digitalinvitro/micro6502/pic/load_bin_menu.jpg

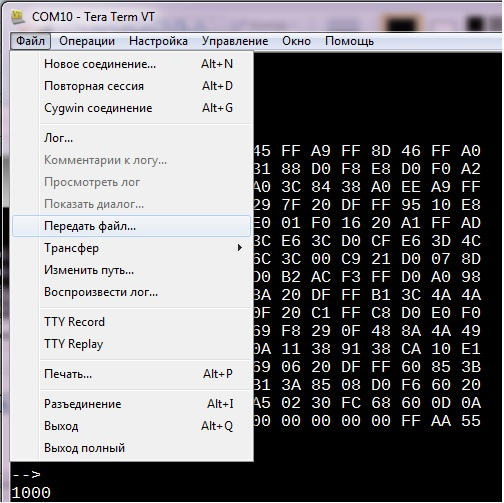
pic/load_bin_menu.jpg
